qt22/12-Vdc-Power-Supply/DC_DC converter/LT1083 LDO.asc

C1: cap; 10µ
C2: cap; 10µ
D1: LED; W5AP-LZMZ-5K8L
D2: schottky; 1N5818
R1: res; 100
R2: res; 866
R3: res; 499
U1: LT1083
V1: voltage; PWL(0 0 1 27)
Named nets: 0, Vout
.tran 2
